skagmo/multitrx/documentation/img/Antenna/1.jpg

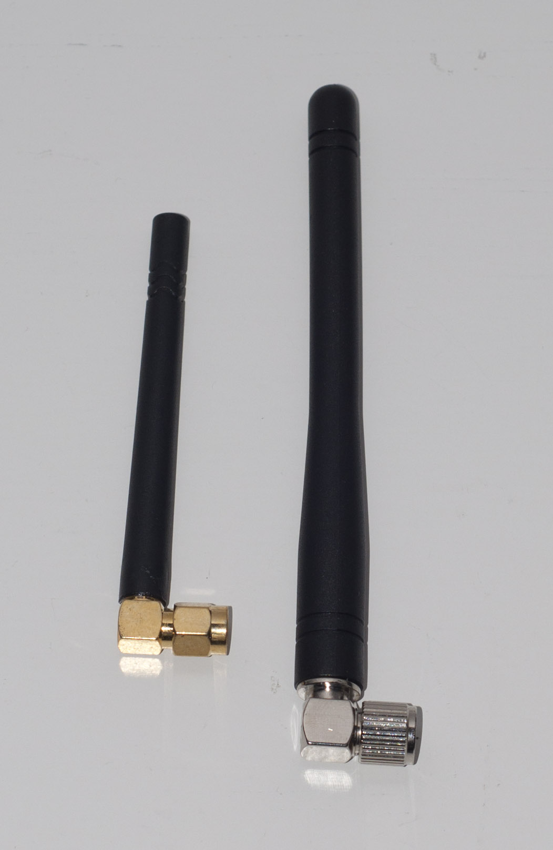
documentation/img/Antenna/1.jpg
