skagmo/multitrx/documentation/img/Antenna/2.jpg

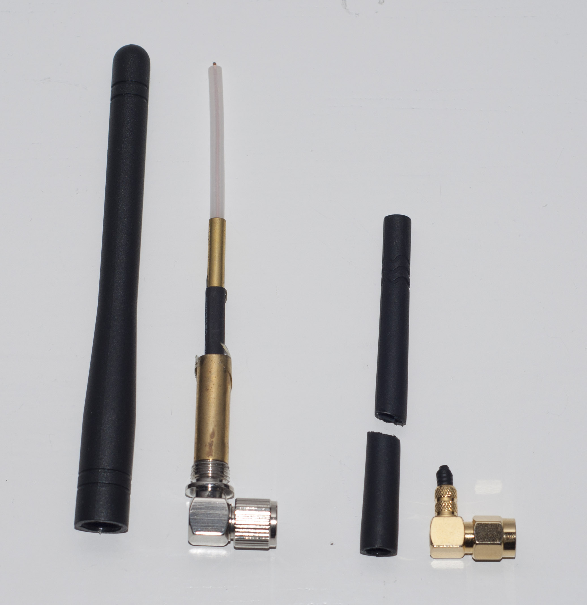
documentation/img/Antenna/2.jpg
