skagmo/multitrx/documentation/img/Antenna/3.jpg

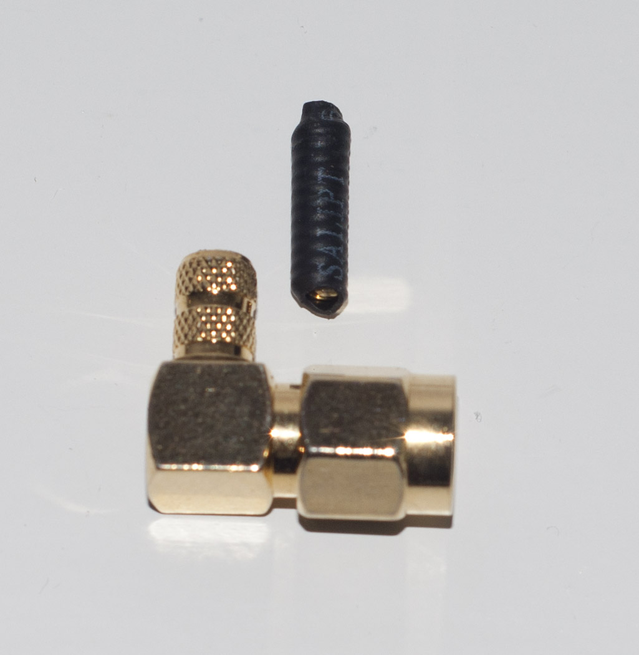
documentation/img/Antenna/3.jpg
