skagmo/multitrx/documentation/img/data.jpg

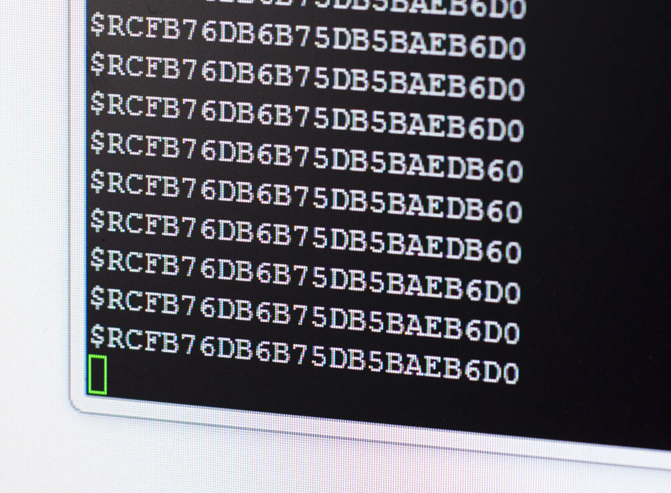
documentation/img/data.jpg
