skagmo/multitrx/documentation/img/doro_mag.jpg

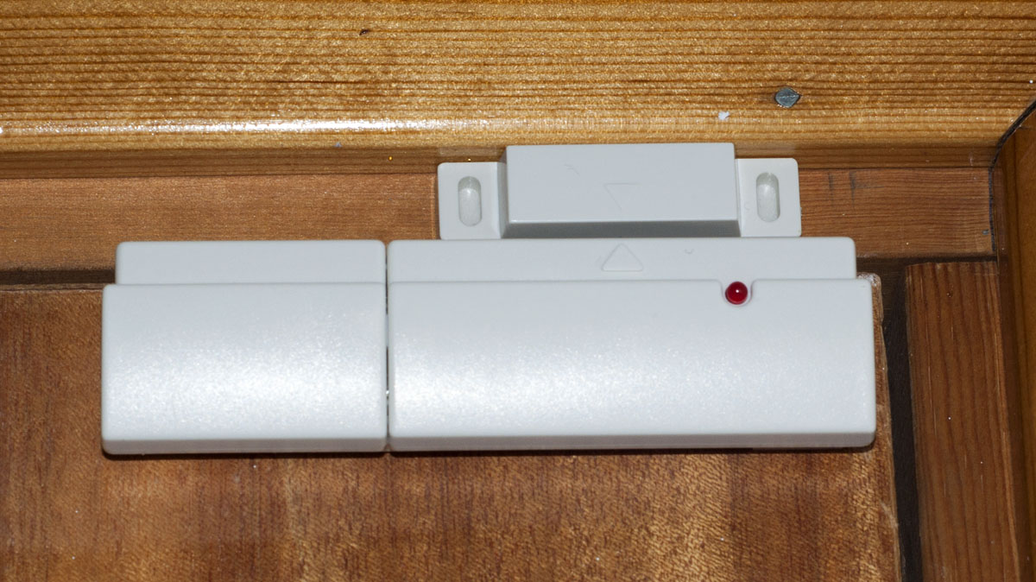
documentation/img/doro_mag.jpg
