skagmo/multitrx/documentation/img/esic.JPG

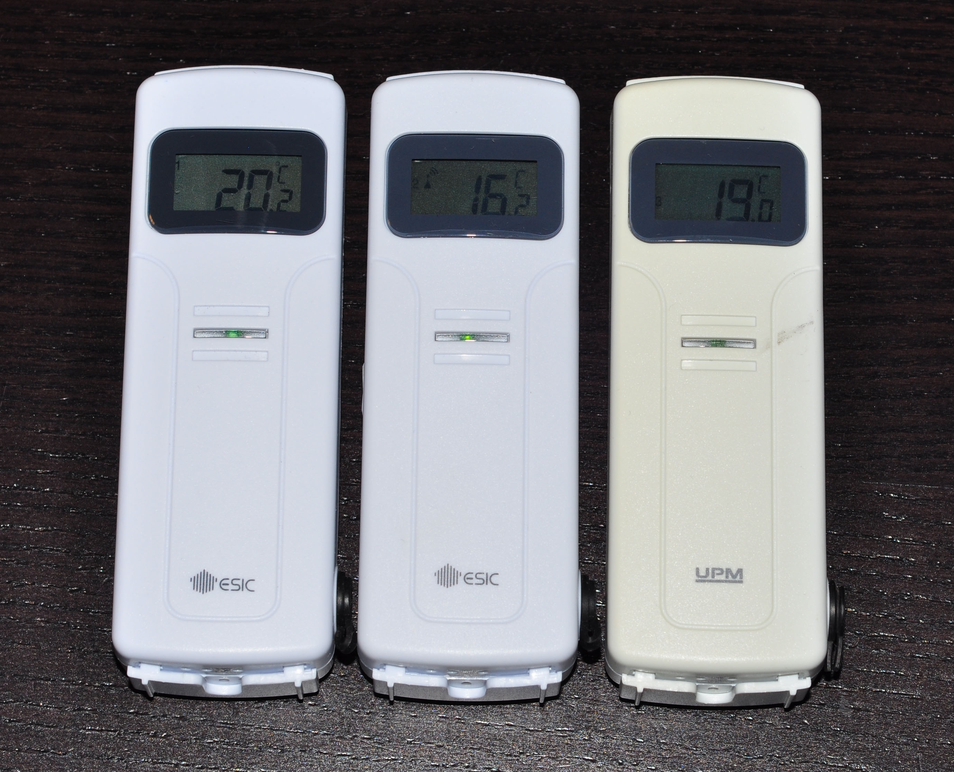
documentation/img/esic.JPG
