skagmo/multitrx/documentation/img/ism-transceiver v2/1.jpg

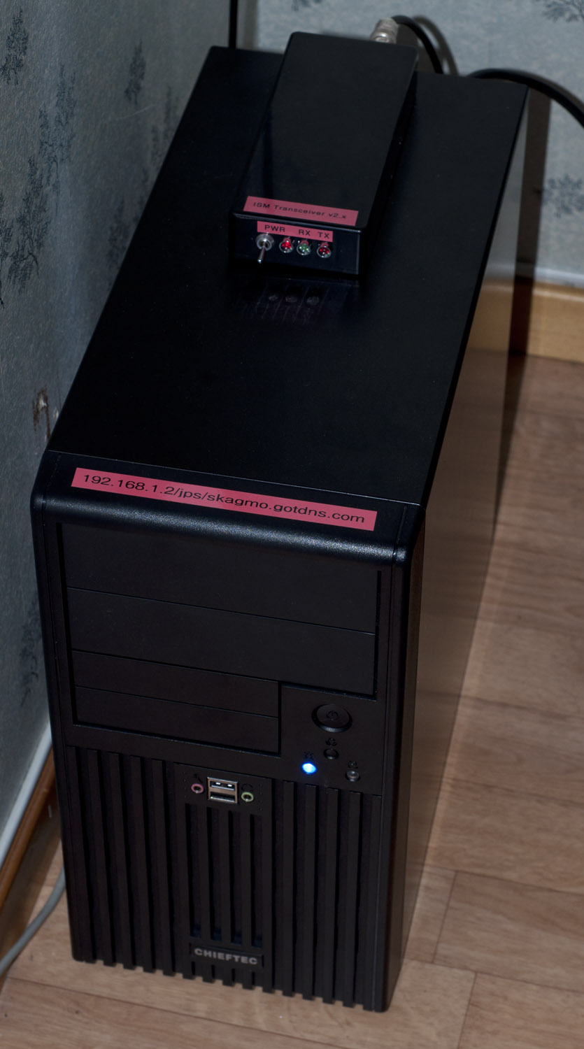
documentation/img/ism-transceiver v2/1.jpg
