skagmo/multitrx/documentation/img/ism-transceiver v2/2.jpg

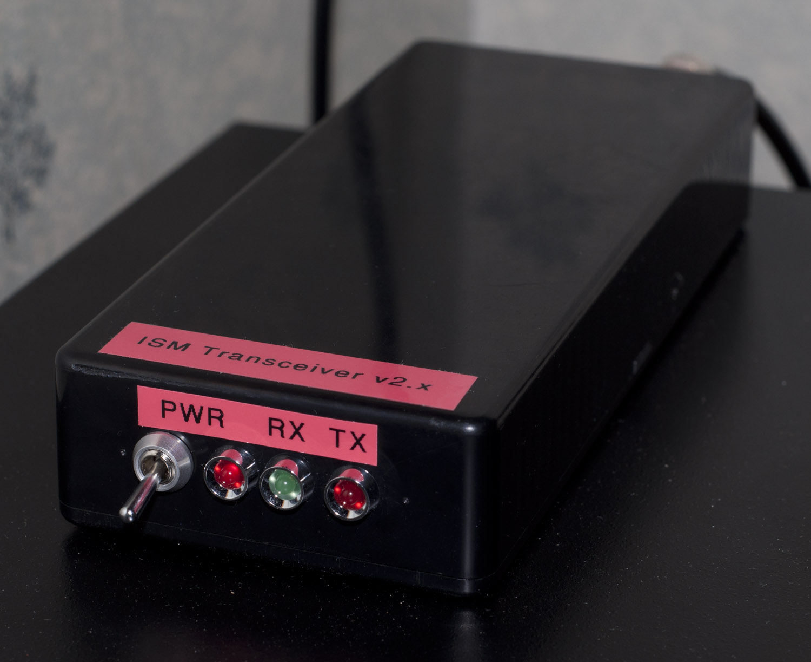
documentation/img/ism-transceiver v2/2.jpg
