skagmo/multitrx/documentation/img/ism-transceiver v2/3.jpg

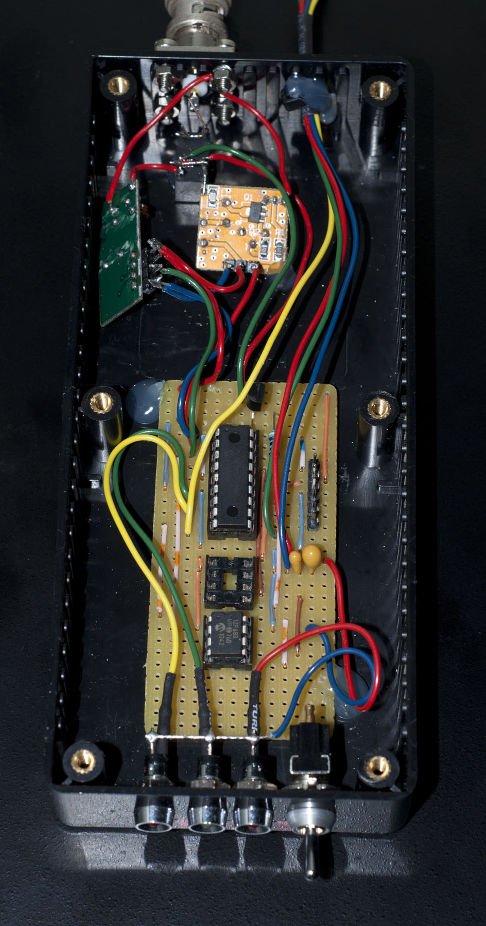
documentation/img/ism-transceiver v2/3.jpg
