skagmo/multitrx/documentation/img/ism-transceiver v2/DSC_0010.jpg

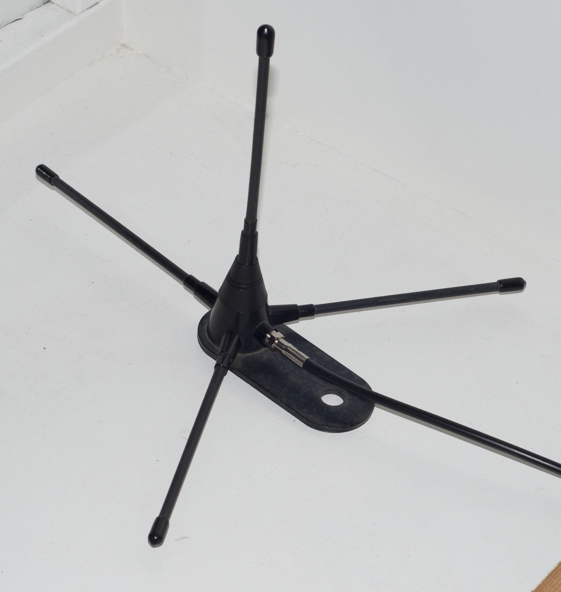
documentation/img/ism-transceiver v2/DSC_0010.jpg
