skagmo/multitrx/documentation/img/ism-transceiver.jpg

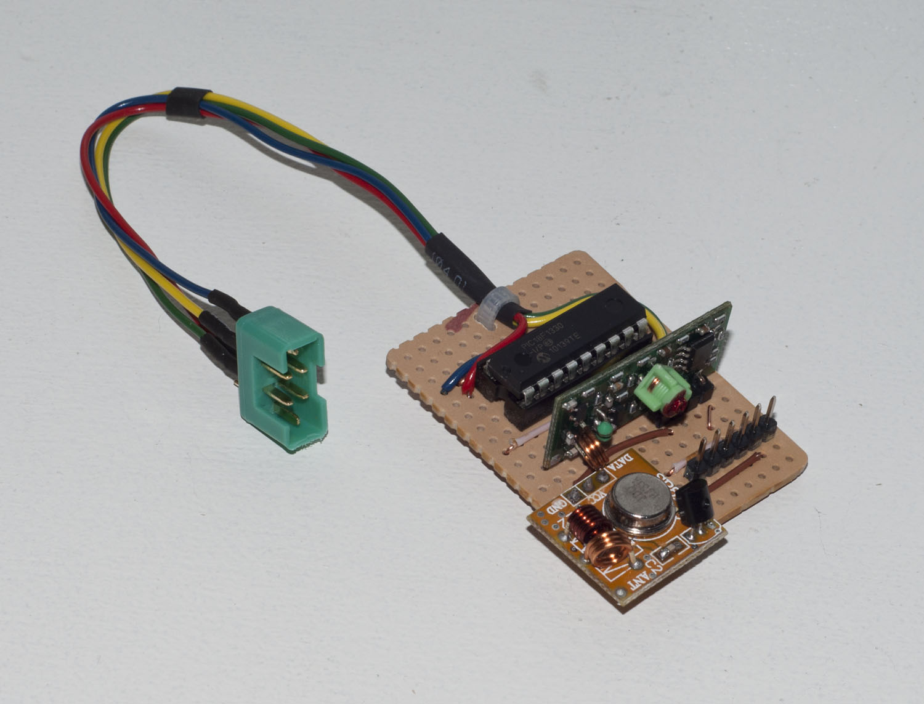
documentation/img/ism-transceiver.jpg
