skagmo/multitrx/documentation/img/MultiTRX HW1.0/5xhw10.jpg

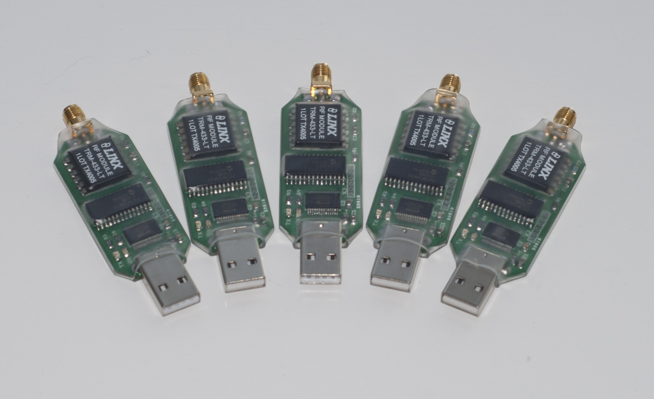
documentation/img/MultiTRX HW1.0/5xhw10.jpg
