skagmo/multitrx/documentation/img/MultiTRX HW1.0/hw10.jpg

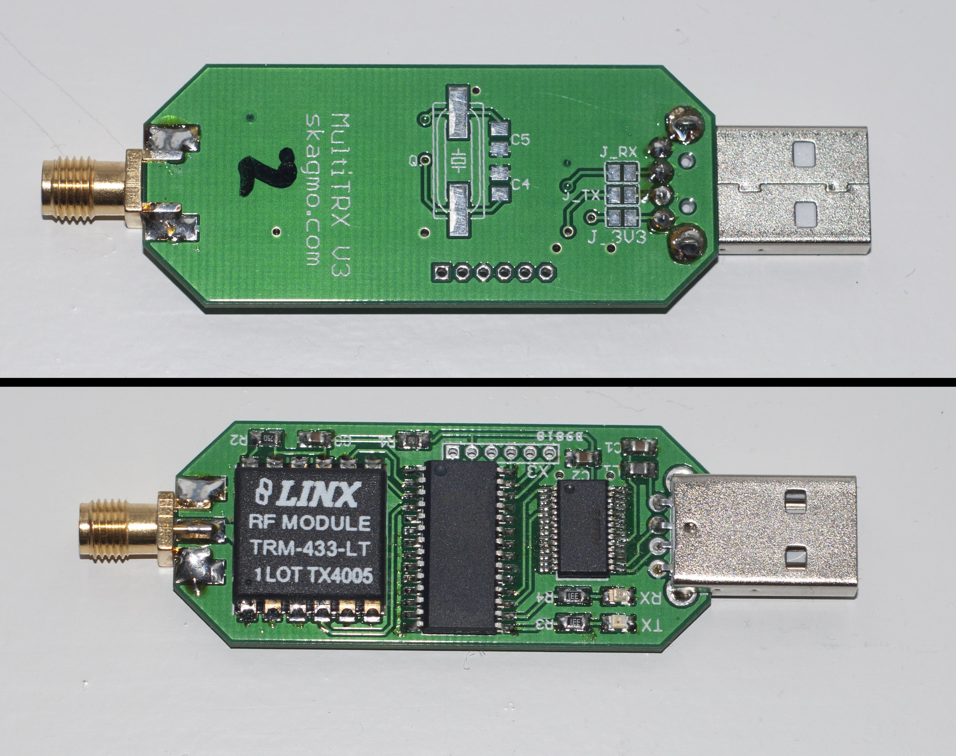
documentation/img/MultiTRX HW1.0/hw10.jpg
