skagmo/multitrx/documentation/img/MultiTRX HW1.1/1xhw11.jpg

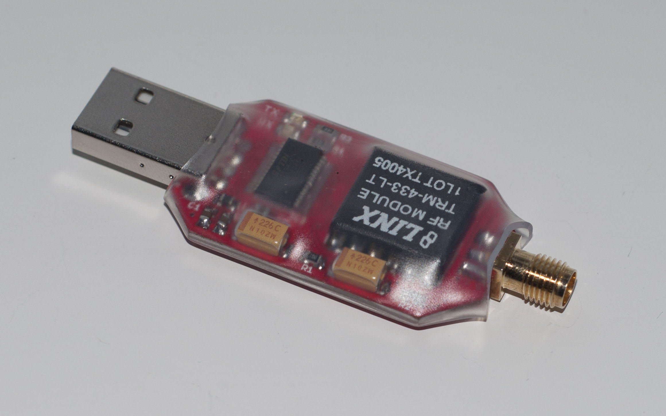
documentation/img/MultiTRX HW1.1/1xhw11.jpg
