skagmo/multitrx/documentation/img/MultiTRX HW1.1/hw11.jpg

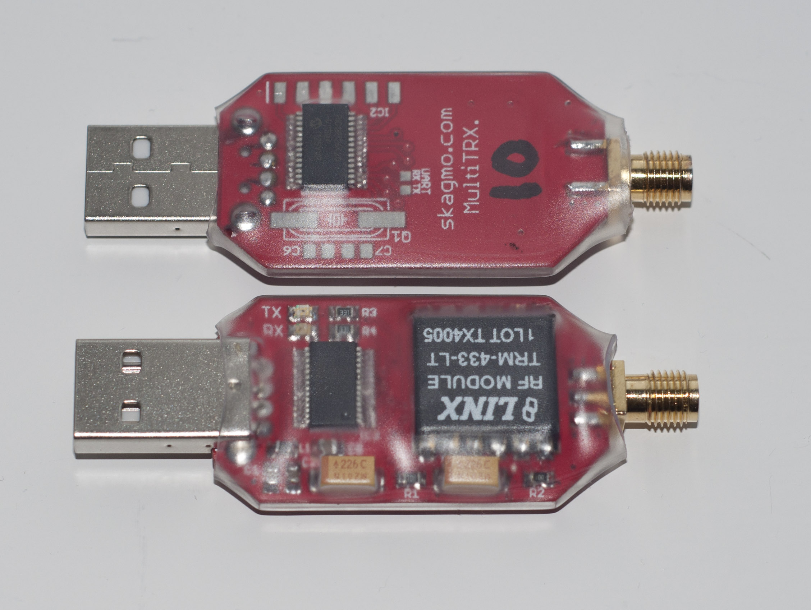
documentation/img/MultiTRX HW1.1/hw11.jpg
