skagmo/multitrx/documentation/img/MultiTRX HW1.1/hw11packed.jpg

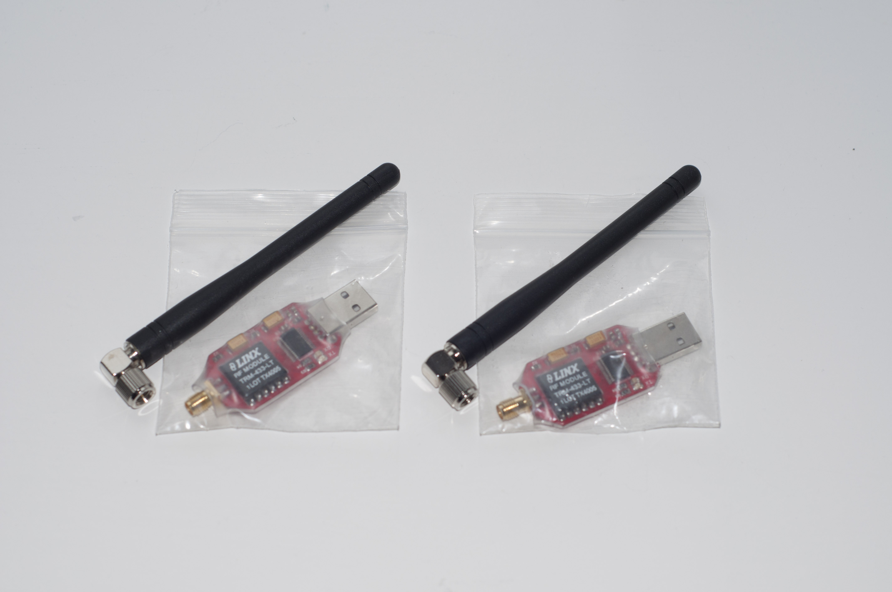
documentation/img/MultiTRX HW1.1/hw11packed.jpg
