skagmo/multitrx/documentation/img/MultiTRX HW1.1/mtrx_klump.jpg

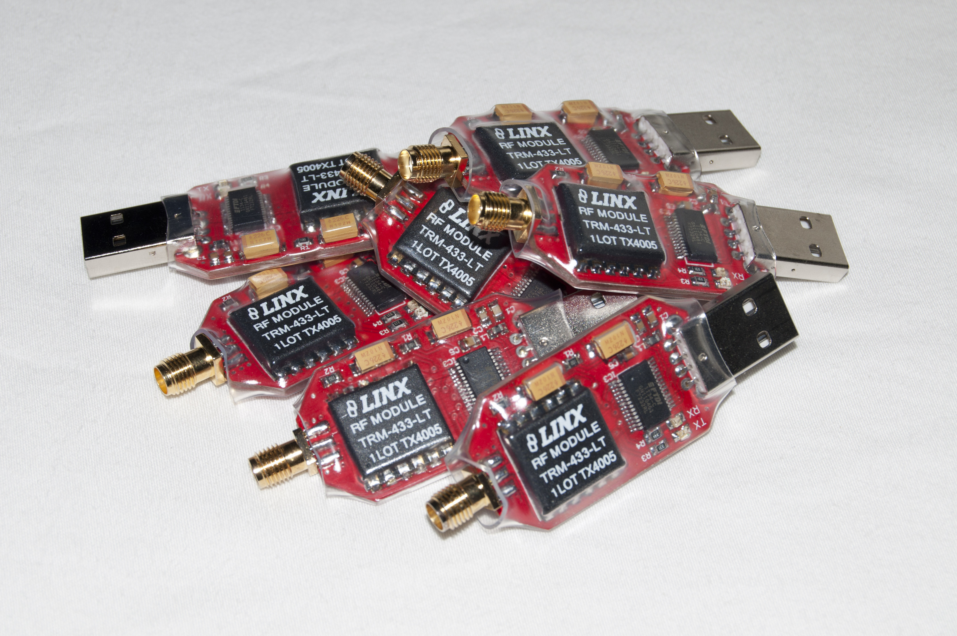
documentation/img/MultiTRX HW1.1/mtrx_klump.jpg
