skagmo/multitrx/documentation/img/MultiTRX HW1.1/mtrx_rekke.jpg

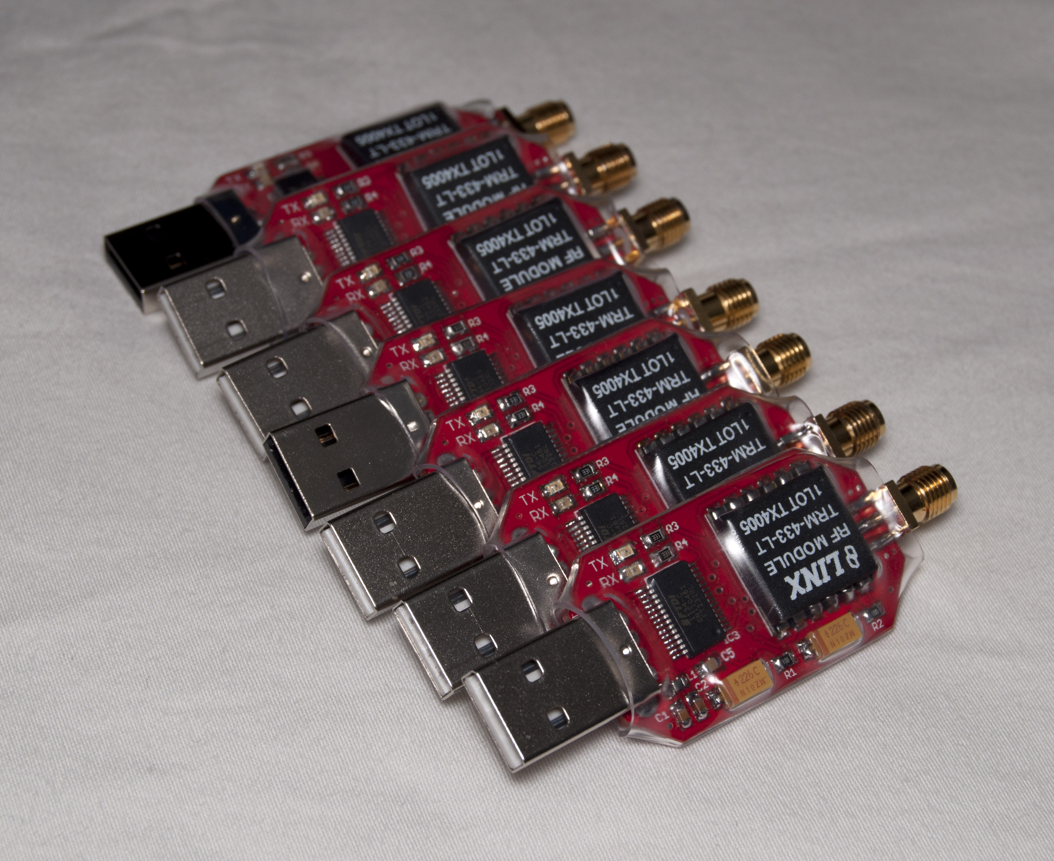
documentation/img/MultiTRX HW1.1/mtrx_rekke.jpg
