skagmo/multitrx/documentation/img/MultiTRX proto/1.jpg

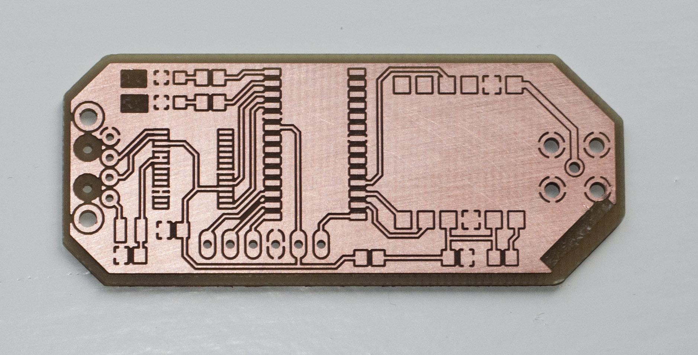
documentation/img/MultiTRX proto/1.jpg
