skagmo/multitrx/documentation/img/MultiTRX proto/2.jpg

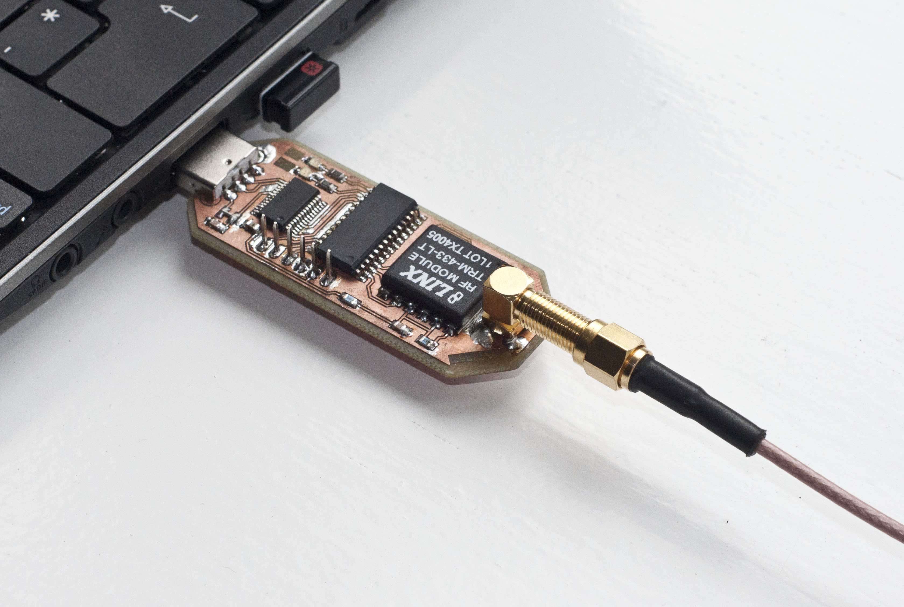
documentation/img/MultiTRX proto/2.jpg
