skagmo/multitrx/documentation/img/MultiTRX proto/3.jpg

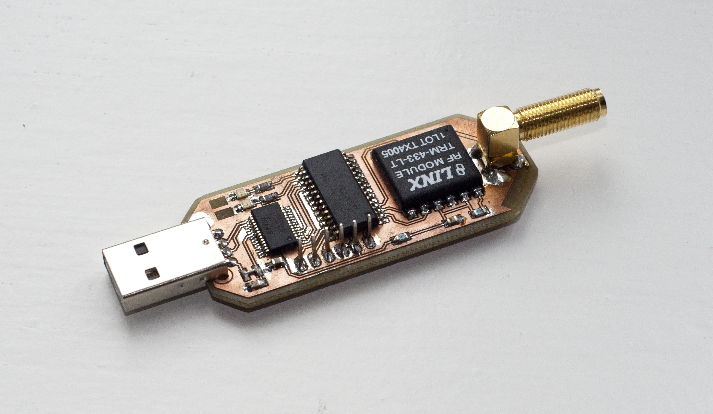
documentation/img/MultiTRX proto/3.jpg
