skagmo/multitrx/documentation/img/nexa_innbygg.jpg

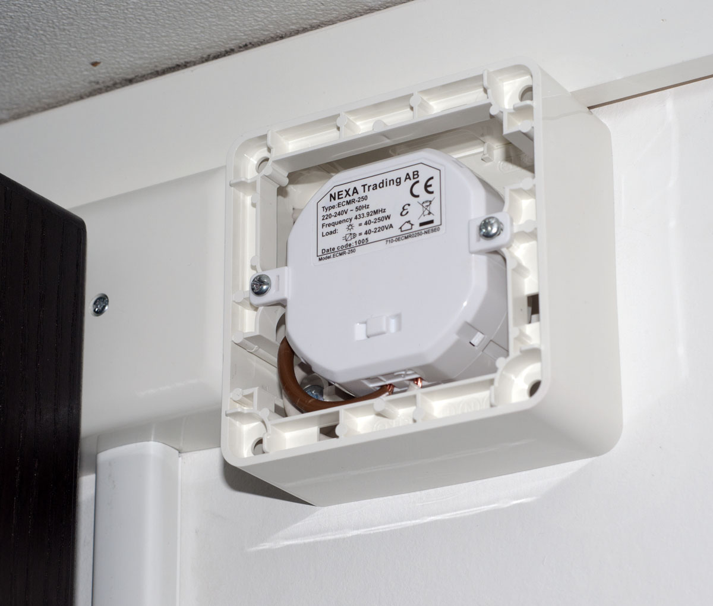
documentation/img/nexa_innbygg.jpg
