skagmo/multitrx/documentation/img/php/device1.jpg

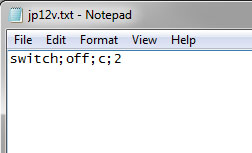
documentation/img/php/device1.jpg
