skagmo/multitrx/documentation/img/php/device2.jpg

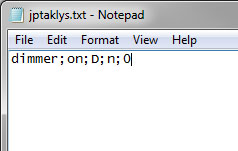
documentation/img/php/device2.jpg
