skagmo/multitrx/documentation/img/php/inst1rot.jpg

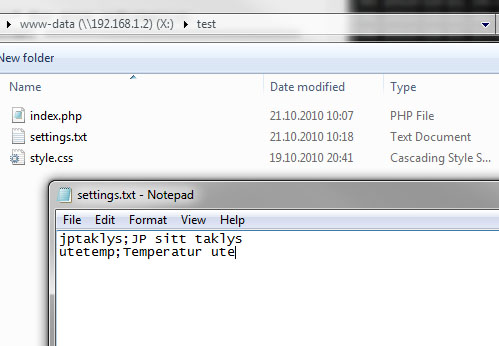
documentation/img/php/inst1rot.jpg
