skagmo/multitrx/documentation/img/php/inst1web.jpg

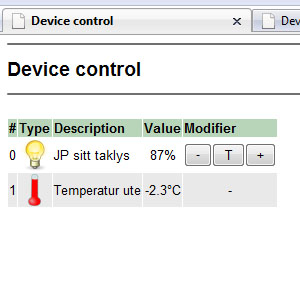
documentation/img/php/inst1web.jpg
