skagmo/multitrx/documentation/img/php/settings1.jpg

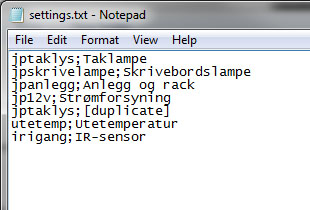
documentation/img/php/settings1.jpg
