skagmo/multitrx/documentation/img/phpsoftware.jpg

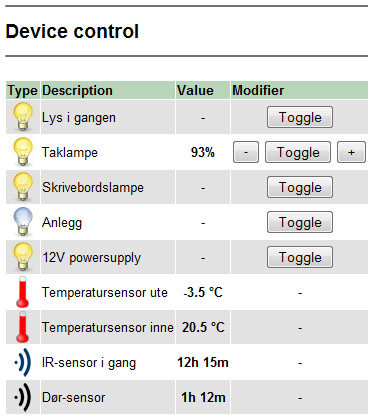
documentation/img/phpsoftware.jpg
