skagmo/multitrx/documentation/img/stikk.jpg

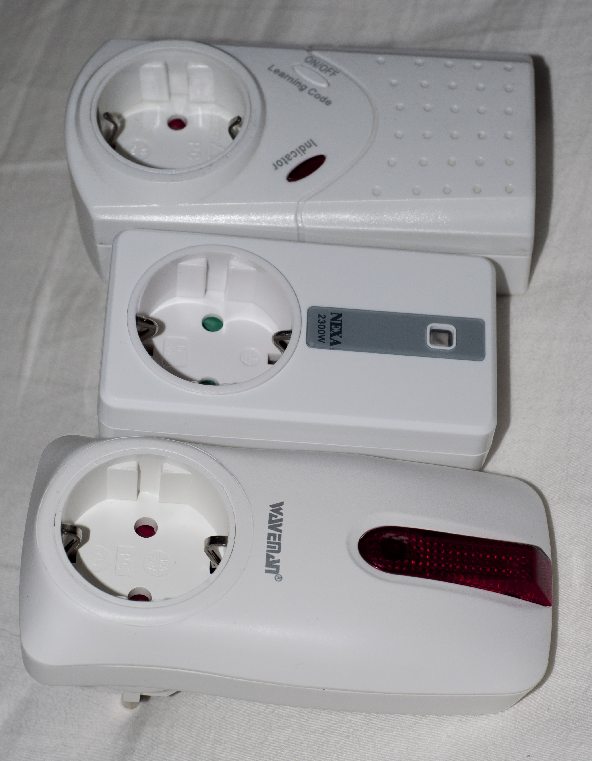
documentation/img/stikk.jpg
