skagmo/multitrx/pcb/1.1.png

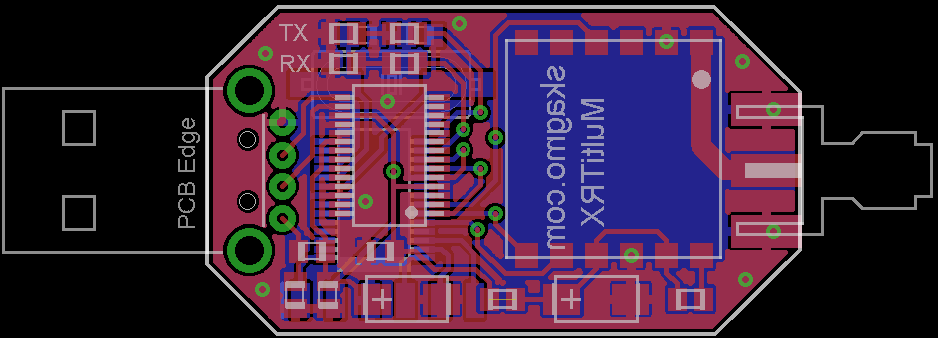
pcb/1.1.png
