skagmo/multitrx/reverse-engineering/NEXA code/code-0-1-on.png

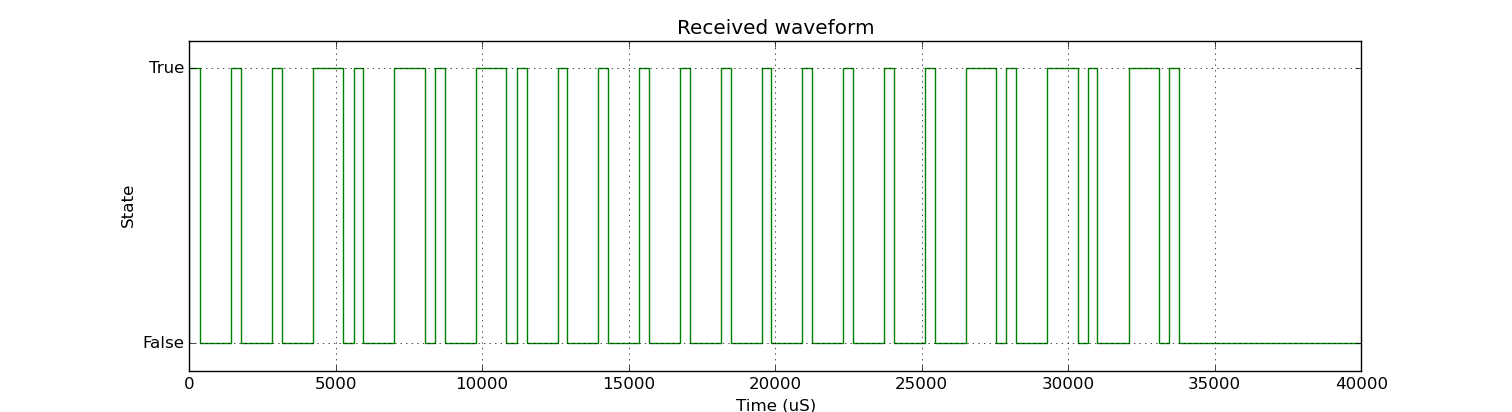
reverse-engineering/NEXA code/code-0-1-on.png
