skagmo/multitrx/reverse-engineering/NEXA learning/figure_1.png

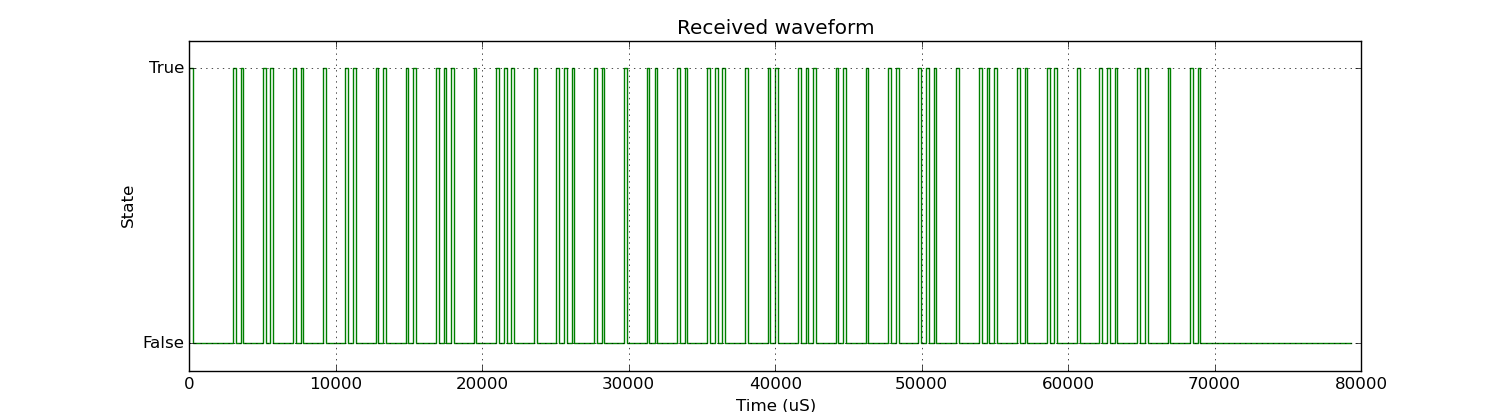
reverse-engineering/NEXA learning/figure_1.png
