skagmo/multitrx/reverse-engineering/NEXA learning/figure_2.png

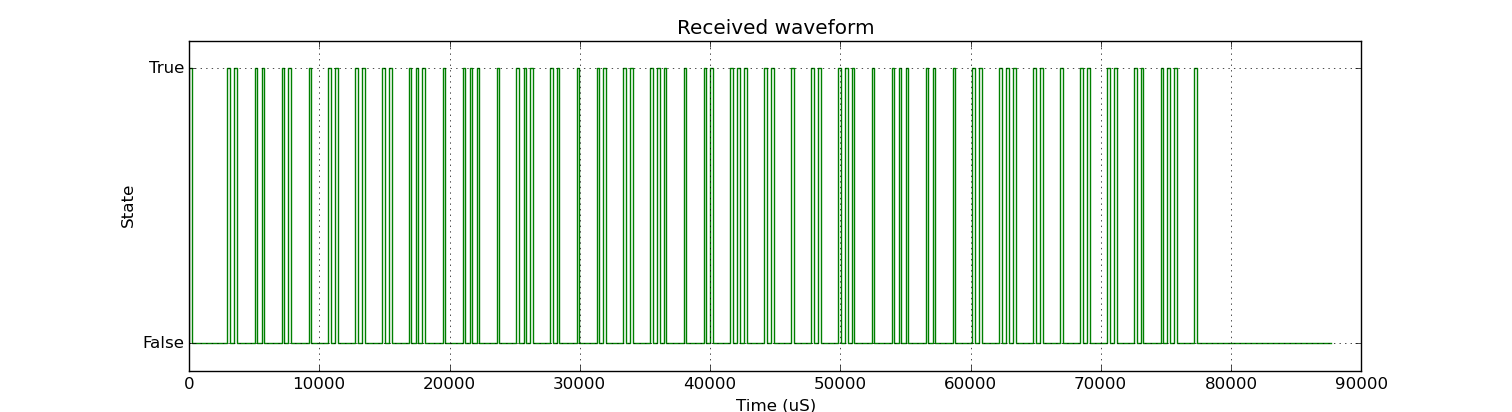
reverse-engineering/NEXA learning/figure_2.png
