skagmo/multitrx/firmware/bootloader-and-compiled/bootloader-guide.png

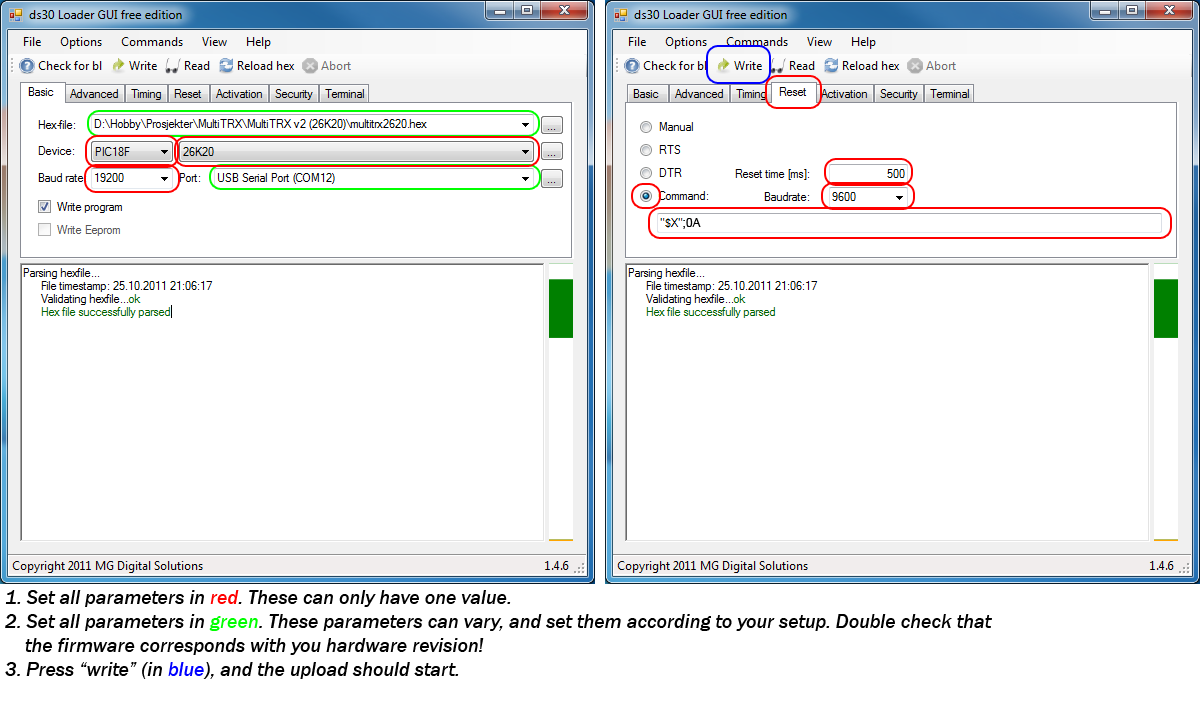
firmware/bootloader-and-compiled/bootloader-guide.png
